periode/music-frame/workshop/media/20200308_proto_01.jpg

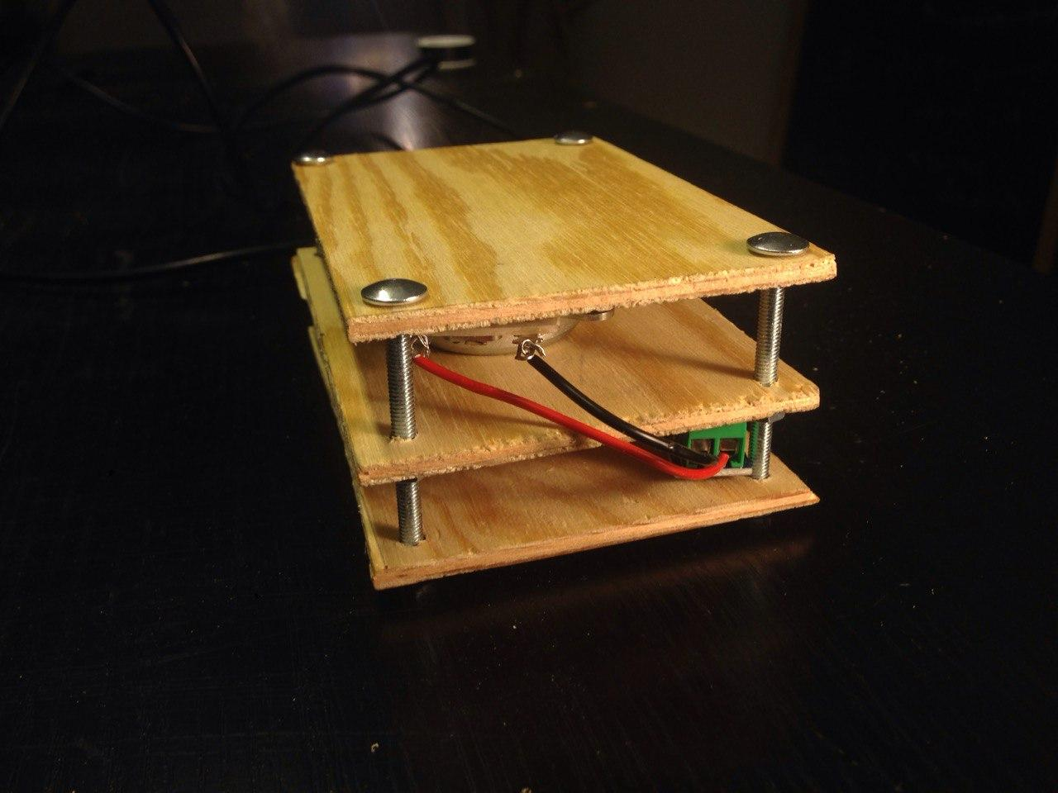
workshop/media/20200308_proto_01.jpg
