periode/music-frame/workshop/media/20200308_proto_04.jpg

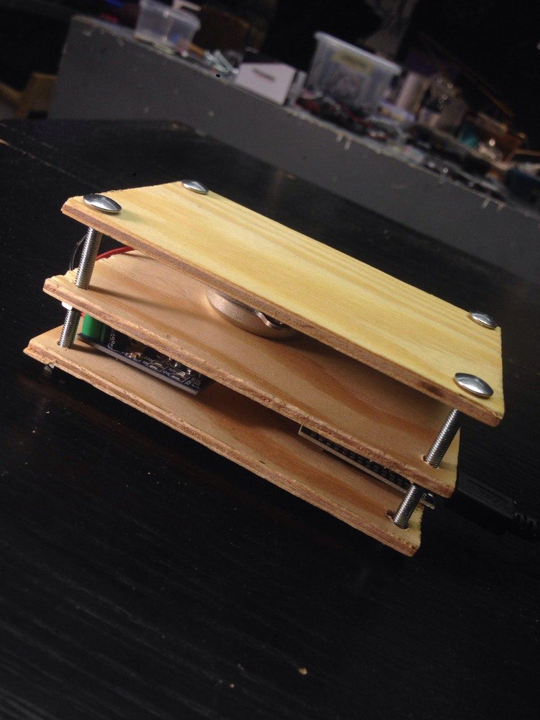
workshop/media/20200308_proto_04.jpg
